FABcamp/SimonGPIO2.0/Project Case Files/Solidworks Files/Components/Screw.SLDPRT

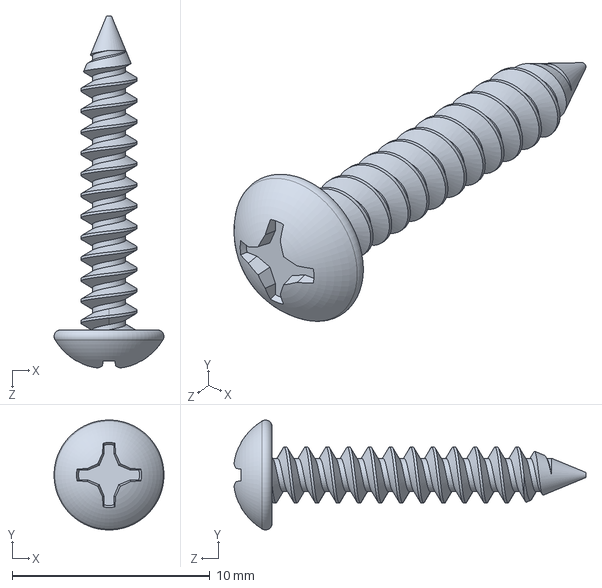
[picture p22: CAD file, 2015-06-27]
Project Case Files/Solidworks Files/Components/Screw.SLDPRT
5.56 x 5.56 x 17.8 mm
